ciruu1/SMA_LAMP/DOCS/SysML/SE_LAMP/image2.png

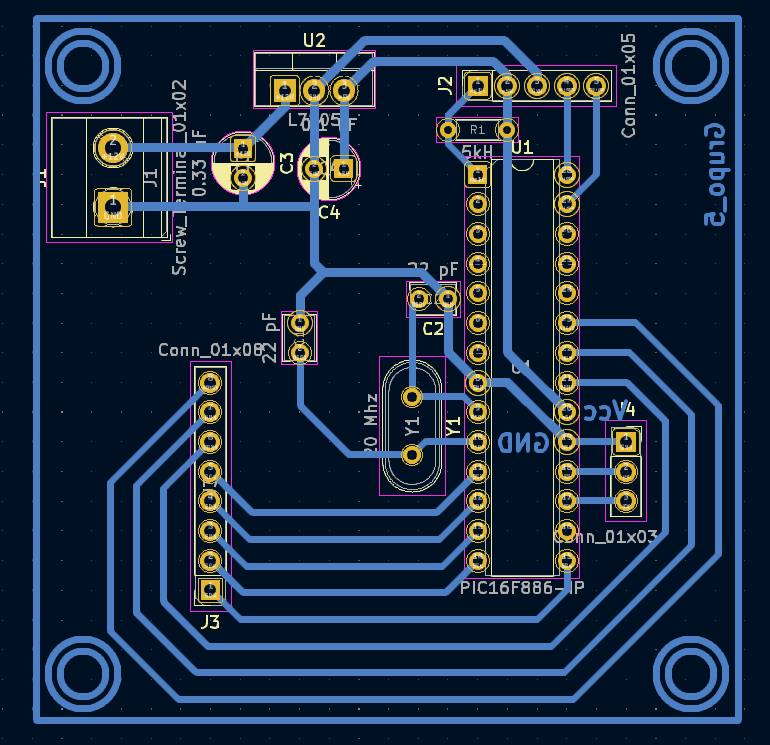
DOCS/SysML/SE_LAMP/image2.png
